AndreasDev05/AntikytheraVQE24/Digi_Uhr/Includes/digi_clock_alarm_fkt.h

/*
 * digi_clock_alarm_fkt.h
 *
 *  Created on: 21.01.2021
 *      Author: andi
 */

#ifndef INCLUDES_DIGI_CLOCK_ALARM_FKT_H_
#define INCLUDES_DIGI_CLOCK_ALARM_FKT_H_

void AlarmBeep(void);
void AlarmBell(void);
void CalcuAlarmSequence(void);
void InitializeAlarm(void);

#endif /* INCLUDES_DIGI_CLOCK_ALARM_FKT_H_ */
