AndreasDev05/AntikytheraVQE24/Digi_Uhr/Includes/digi_clock_isr.c

/*
 * digi_clock_isr.c
 *
 *  Created on: 05.05.2020
 *      Author: andi
 */

#include <stdbool.h>
#include <stdint.h>
#include <msp430.h>
#include <msp430f5529.h>
#include "digi_clock.h"
#include "digi_clock_isr.h"

// Variablen in den Interruptfkt. -----
// Variables for display management
    // to reduce flicker save the display in this memory
    // pointer to the active displaymemory


#pragma vector=TIMER0_A0_VECTOR
__interrupt void TIMER0_A0_ISR(void)
{
    extern volatile uint8_t is_sec;
    TA0CCR0   += TIME_PERIOD_SEC;
    is_sec++;
    __no_operation();                         // For debugger

}

#pragma vector=TIMER0_A1_VECTOR
__interrupt void TIMER0_A1_ISR(void)
{
    extern volatile uint8_t is_msec,is_msec2,is_100ms2,is_300ms;
    switch (__even_in_range(TA0IV, 14))
    {
    case 0:
        break;
    case 2:
        TA0CCR1 += TIME_PERIOD_1;          // Add Offset to CCR1
        is_msec++;
        break;
    case 4:
        TA0CCR2 += TIME_PERIOD_2;                // Add Offset to CCR2
        is_msec2++;
//               SIGNALS_OUT ^= LED_SEC;        // Toggle P7.3
        break;
    case 6:
        TA0CCR3 += TIME_PERIOD_300ms;
        is_300ms++;
        break;                         // CCR3 not used
    case 8:
        TA0CCR4 += TIME_PERIOD_100ms2;
        is_100ms2++;
        break;                         // CCR4 not used
    case 10:
        break;                         // CCR5 not used
    case 12:
        break;                         // Reserved not used
    case 14:                                // overflow
        break;
    default:
        break;
    }

}

#pragma vector=TIMER1_A0_VECTOR
__interrupt void TIMER1_A0_ISR(void)
{
    extern uint8_t disp_point, disp_point_blink;
    extern volatile uint8_t *disp_out_point;
    extern volatile uint8_t disp_count;

// the brightness of the display: it is recommended to use values between 10 and "TIME_PERIOD_DIGT"-10.
   extern volatile uint16_t  disp_brightness;  // brightness

   uint8_t temp_DP_mask;

    TA1CCR0         += TIME_PERIOD_DIGT;
//    SIGNALS_OUT    |= LED_SEC;                            // switch P7.3 on
    SIGNALS_OUT    |= DARK;
    DISPLAY_OUT = *(disp_out_point+disp_count);
/*  switching decimal point */
    temp_DP_mask = *(disp_out_point+disp_count) >> 4;
    if (disp_point & temp_DP_mask)
    {
        SIGNALS_OUT |= LED_DP;
    }
    else
    {
        SIGNALS_OUT &= ~LED_DP;
    }
    if (disp_point & MINUS_PNT)
    {
        SIGNALS_OUT |= LED_MINUS;
    }
    else
    {
        SIGNALS_OUT &= ~LED_MINUS;
    }
    if (disp_point & SEC_PNT)
    {
        SIGNALS_OUT |= LED_SEC;
    }
    else
    {
        SIGNALS_OUT &= ~LED_SEC;
    }
//    if (disp_count < 3) disp_count++; else disp_count = 0;
    disp_count++;
    disp_count &= 0x03;

    //  Set the Compare-Register and starts the interrupt to adjust the brightness
    TA1CCR1  = TA1R + disp_brightness;     // brightness
    TA1CCTL1 = CCIE;            // CCR1 interrupt enabled
}

#pragma vector=TIMER1_A1_VECTOR
__interrupt void TIMER1_A1_ISR(void)
{
    extern uint8_t is_100ms;
    switch (__even_in_range(TA1IV, 14))
    {
    case 0:
        break;
    case 2:
        TA1CCTL1 &= ~CCIE;             // CCR1 interrupt disabled
//        SIGNALS_OUT &= ~LED_SEC;      // switch P7.3 off
        SIGNALS_OUT    &= ~(DARK | LED_SEC | LED_MINUS);
        break;
    case 4:
        TA1CCR2 += TIME_PERIOD_100ms;  // Add Offset to CCR3
        is_100ms++;
        break;
    case 6:
        break;                         // CCR2 not used
    case 8:
        break;                         // CCR4 not used
    case 10:
        break;                         // CCR5 not used
    case 12:
        break;                         // Reserved not used
    case 14:                                // overflow
        break;
    default:
        break;
    }

}

#pragma vector=ADC12_VECTOR
__interrupt void ADC12ISR (void)
{
    // Variables for ADC12
  extern volatile uint16_t adc_out_raw[8];
  extern bool adc_conv_ready;    // ready
  static uint8_t adc_m_count = 8;
  switch(__even_in_range(ADC12IV,34))
  {
  case  0: break;                           // Vector  0:  No interrupt
  case  2: break;                           // Vector  2:  ADC overflow
  case  4: break;                           // Vector  4:  ADC timing overflow
  case  6:                                  // Vector  6:  ADC12IFG0
    adc_m_count--;
    adc_out_raw[adc_m_count] = ADC12MEM0;                   // Move results, IFG is cleared
    if (adc_m_count == 0)
    {
//        CONTROL_OUT &= ~(TURNON_OPA | TURNON_RELAY);
        adc_m_count = 8;
        ADC12CTL1 &=  ~(0x06);       //
        ADC12CTL0 &=  ~ADC12SC;            // switch ADC-process off
        ADC12CTL0 &=  ~ADC12ENC;
        adc_conv_ready = true;
    }
    break;
  case  8: break;                           // Vector  8:  ADC12IFG1
  case 10: break;                           // Vector 10:  ADC12IFG2
  case 12: break;                           // Vector 12:  ADC12IFG3
  case 14: break;                           // Vector 14:  ADC12IFG4
  case 16: break;                           // Vector 16:  ADC12IFG5
  case 18: break;                           // Vector 18:  ADC12IFG6
  case 20: break;                           // Vector 20:  ADC12IFG7
  case 22: break;                           // Vector 22:  ADC12IFG8
  case 24: break;                           // Vector 24:  ADC12IFG9
  case 26: break;                           // Vector 26:  ADC12IFG10
  case 28: break;                           // Vector 28:  ADC12IFG11
  case 30: break;                           // Vector 30:  ADC12IFG12
  case 32: break;                           // Vector 32:  ADC12IFG13
  case 34: break;                           // Vector 34:  ADC12IFG14
  default: break;
  }
}

#pragma vector=PORT1_VECTOR
__interrupt void PORT1_ISR(void)
{
    extern volatile uint8_t btn_is_int_set;
//  temp_p2 = BUTTON_IFG & BUTTON_2;
    if ((P1IFG & BUTTON_1) > 0) {
      btn_is_int_set |= BUTTON_down;
      BUTTON_IFG  &=  ~BUTTON_1;
    }

    if ((P1IFG & BUTTON_2) > 0) {
      btn_is_int_set |= BUTTON_up;
      BUTTON_IFG  &=  ~BUTTON_2;
    }

    if ((P1IFG & BUTTON_3) > 0) {
      btn_is_int_set |= BUTTON_left;
      BUTTON_IFG  &=  ~BUTTON_3;
    }

    if ((P1IFG & BUTTON_4) > 0) {
      btn_is_int_set |= BUTTON_right;
      BUTTON_IFG  &=  ~BUTTON_4;
    }

    if ((P1IFG & BUTTON_5) > 0) {
      btn_is_int_set |= BUTTON_mode;
      BUTTON_IFG  &=  ~BUTTON_5;
    }

    if ((P1IFG & BUTTON_6) > 0) {
      btn_is_int_set |= BUTTON_alarm;
      BUTTON_IFG  &=  ~BUTTON_6;
    }

    //  BUTTON_IFG = 0;
//  BUTTON_IE &= ~BUTTON;            /* Debounce */
//  WDTCTL = WDT_ADLY_250;
//  IFG1 &= ~WDTIFG;                 /* clear interrupt flag */
//  IE1 |= WDTIE;
//  P1OUT^=BIT0;        // toggle P1.0

/*
  if (applicationMode == APP_APPLICATION_MODE)
  {
    tempCalibrated = tempAverage;
    calibrateUpdate  = 1;
  }
  else
  {
    applicationMode = APP_APPLICATION_MODE; // Switch from STANDBY to APPLICATION MODE
    __bic_SR_register_on_exit(LPM3_bits);
  }*/
}
